svenpetersen1965/Joystick-for_commodore_and_atar/top level project/Rev. 0/pictures/3573_joystick_complete.JPG

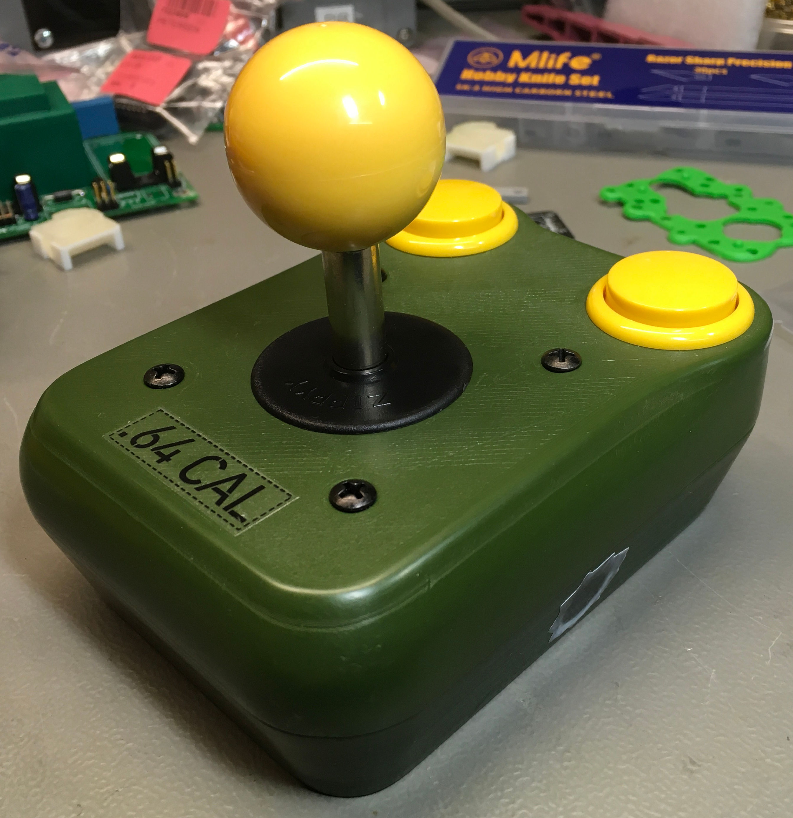
top level project/Rev. 0/pictures/3573_joystick_complete.JPG
