svenpetersen1965/Joystick-for_commodore_and_atar/top level project/Rev. 0/pictures/3600_joystick_rubber_feet.JPG

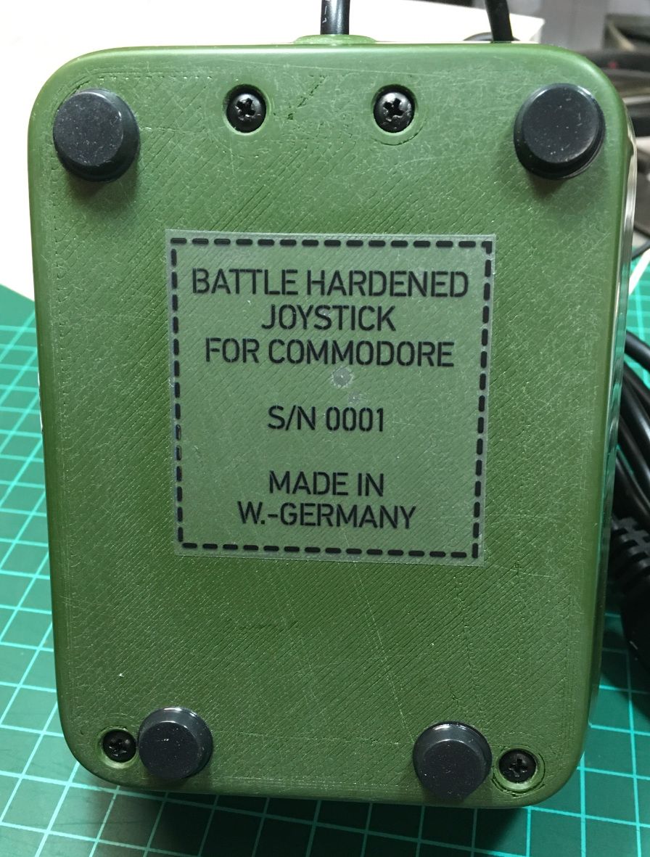
top level project/Rev. 0/pictures/3600_joystick_rubber_feet.JPG
