svenpetersen1965/Joystick-for_commodore_and_atar/top level project/Rev. 0/pictures/Joystick_Simple_Interconnect_pcb.png

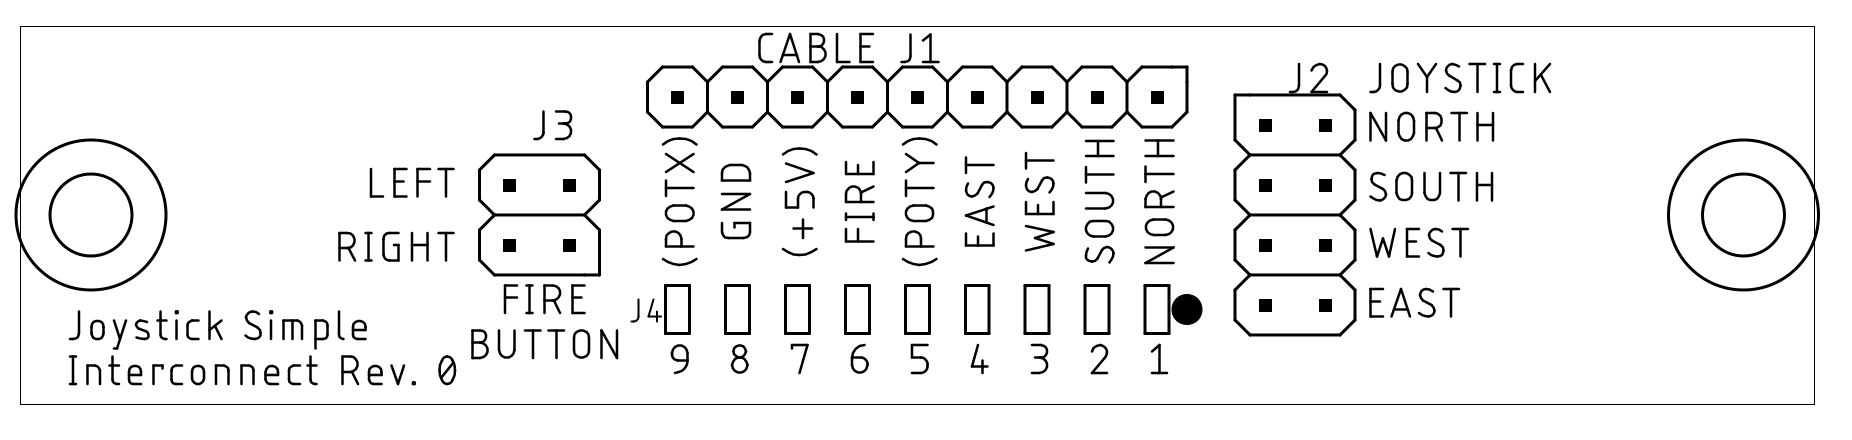
top level project/Rev. 0/pictures/Joystick_Simple_Interconnect_pcb.png
